lrrosa/cronometro-hotwheels/cronometro-arduino/kicad/cronometro-arduino.kicad_sch

## KiCad design cronometro-arduino/kicad/cronometro-arduino.kicad_sch (2026-09-14)

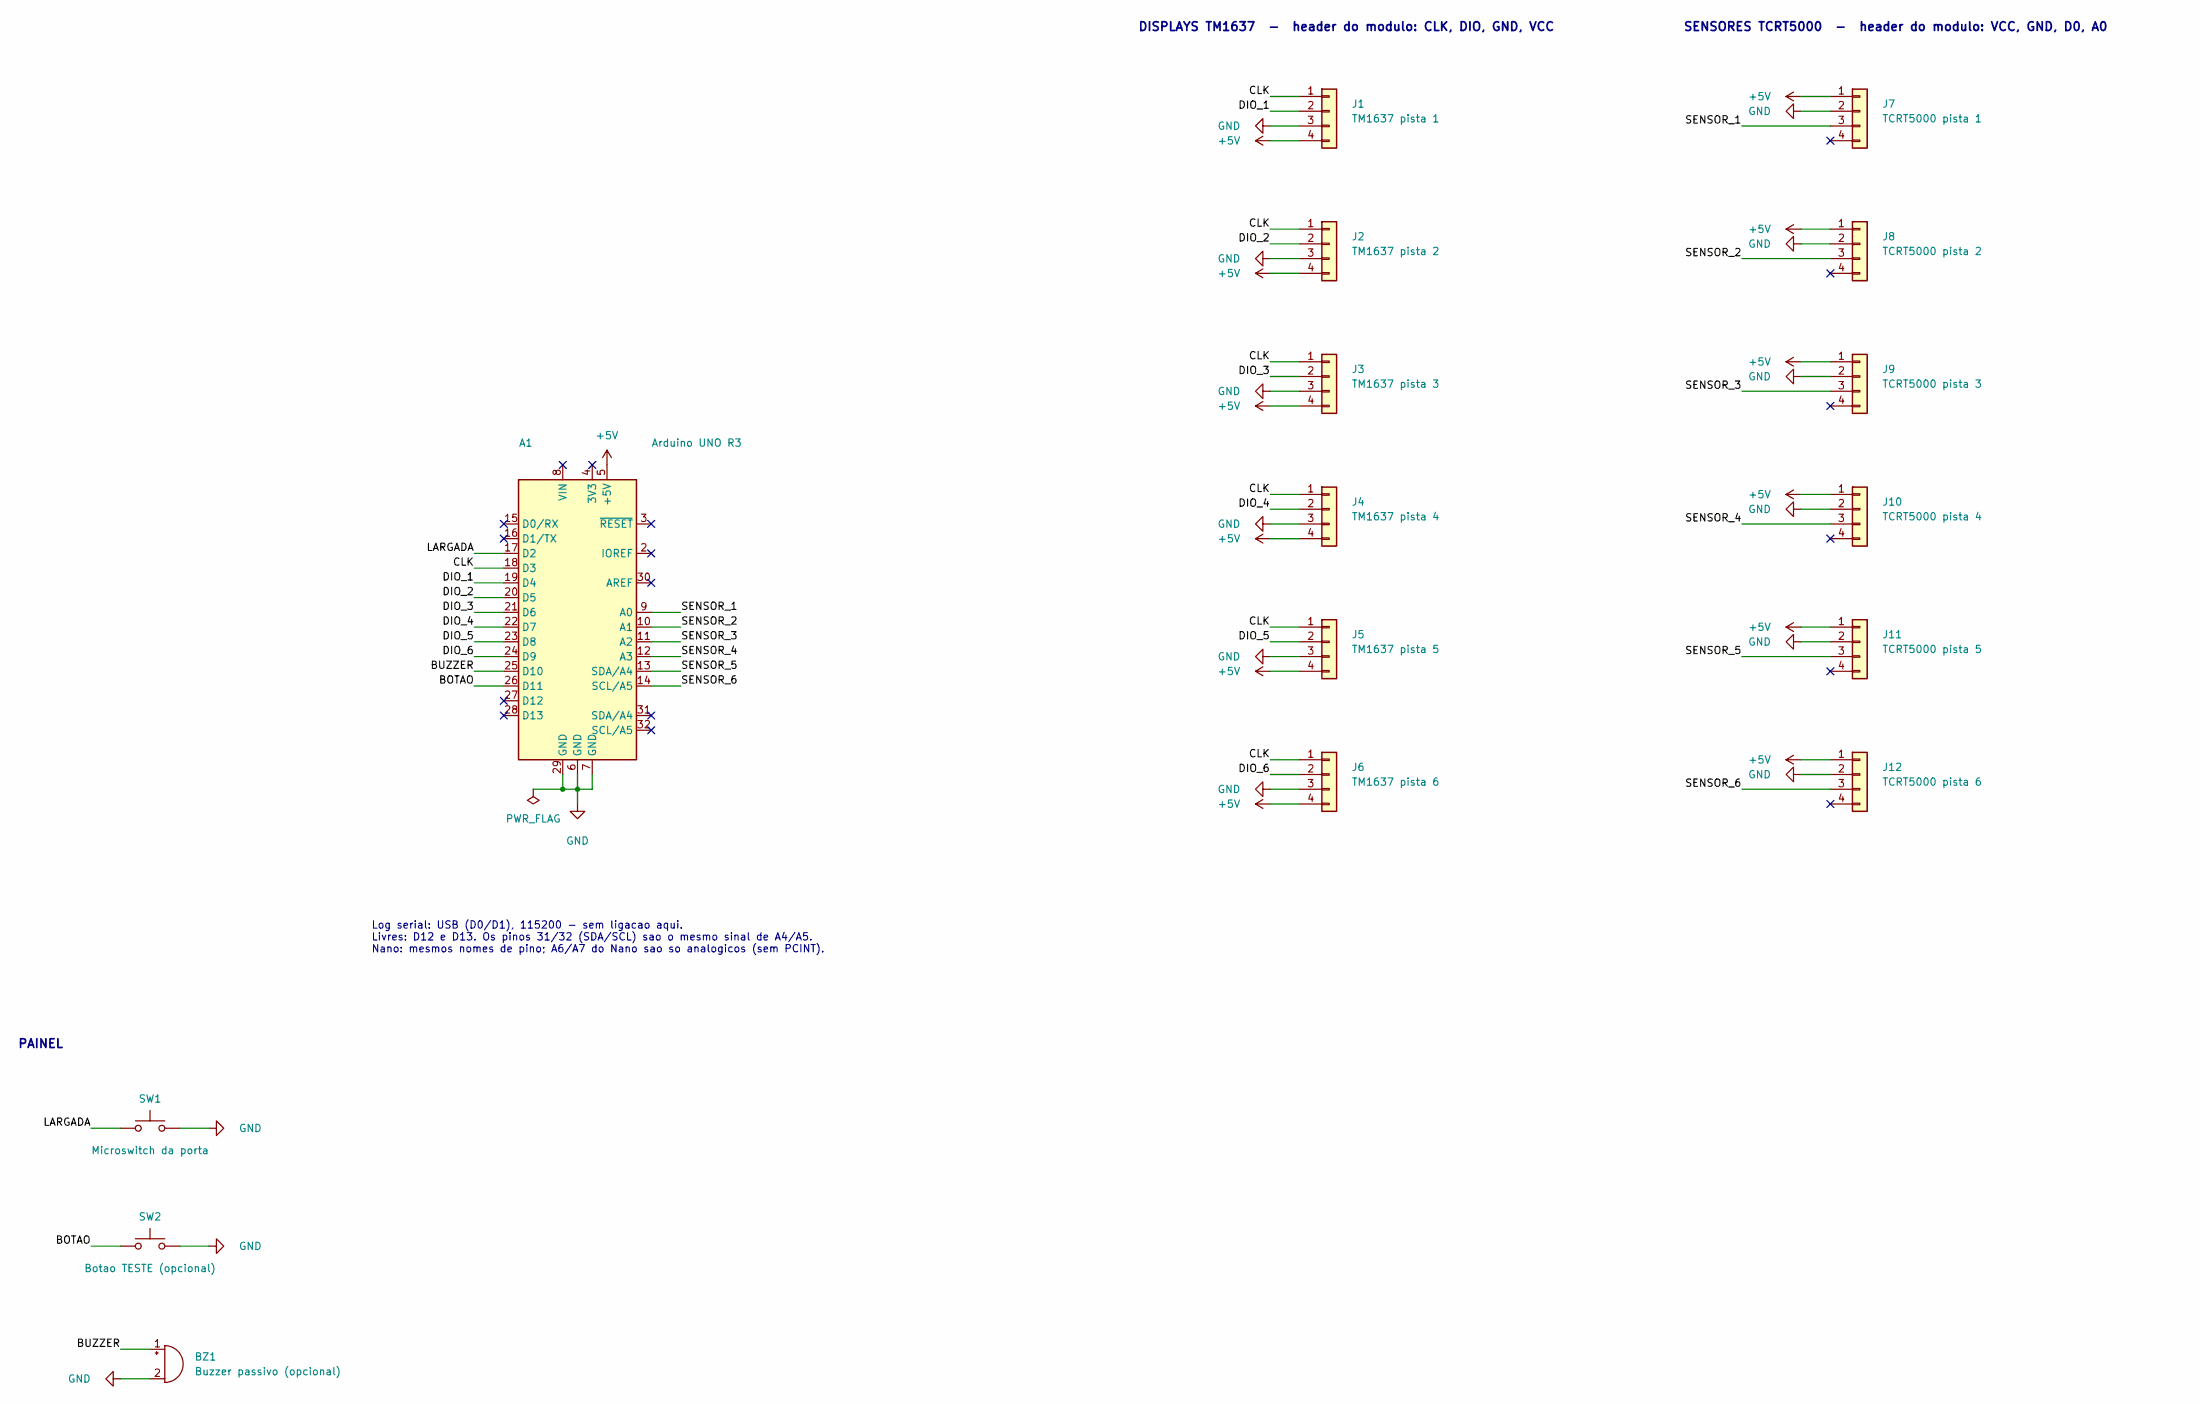
[picture p3: schematic cronometro-arduino.kicad_sch]

Parts:
A1: Arduino UNO R3
BZ1: Buzzer passivo (opcional)
J1: TM1637 pista 1
J2: TM1637 pista 2
J3: TM1637 pista 3
J4: TM1637 pista 4
J5: TM1637 pista 5
J6: TM1637 pista 6
J7: TCRT5000 pista 1
J8: TCRT5000 pista 2
J9: TCRT5000 pista 3
J10: TCRT5000 pista 4
J11: TCRT5000 pista 5
J12: TCRT5000 pista 6
SW1: Microswitch da porta
SW2: Botao TESTE (opcional)

Connections:
+5V: A1.5 (+5V), J1.4, J2.4, J3.4, J4.4, J5.4, J6.4, J7.1, J8.1, J9.1, J10.1, J11.1, J12.1
BOTAO: A1.26 (D11), SW2.1
BUZZER: A1.25 (D10), BZ1.1 (+)
CLK: A1.18 (D3), J1.1, J2.1, J3.1, J4.1, J5.1, J6.1
DIO_1: A1.19 (D4), J1.2
DIO_2: A1.20 (D5), J2.2
DIO_3: A1.21 (D6), J3.2
DIO_4: A1.22 (D7), J4.2
DIO_5: A1.23 (D8), J5.2
DIO_6: A1.24 (D9), J6.2
GND: A1.6 (GND), A1.7 (GND), A1.29 (GND), BZ1.2 (-), J1.3, J2.3, J3.3, J4.3, J5.3, J6.3, J7.2, J8.2, J9.2, J10.2, J11.2, J12.2, SW1.2, SW2.2
LARGADA: A1.17 (D2), SW1.1
SENSOR_1: A1.9 (A0), J7.3
SENSOR_2: A1.10 (A1), J8.3
SENSOR_3: A1.11 (A2), J9.3
SENSOR_4: A1.12 (A3), J10.3
SENSOR_5: A1.13 (SDA/A4), J11.3
SENSOR_6: A1.14 (SCL/A5), J12.3

Notes on the sheet:
Log serial: USB (D0/D1), 115200 - sem ligacao aqui. Livres: D12 e D13. Os pinos 31/32 (SDA/SCL) sao o mesmo sinal de A4/A5. Nano: mesmos nomes de pino; A6/A7 do Nano sao so analogicos (sem PCINT).
DISPLAYS TM1637 - header do modulo: CLK, DIO, GND, VCC
SENSORES TCRT5000 - header do modulo: VCC, GND, D0, A0
PAINEL
